David9248/Tofu-Zero/tofuzero/keymaps/default/ANTIGO CONFIG.txt

#define ENCODER_A_PINS { GP9, GP12 }
#define ENCODER_B_PINS { GP10, GP13 }
