David9248/Tofu-Zero/tofuzero/keymaps/vial/keymap.c

#include QMK_KEYBOARD_H

enum layer_names {
    _0,
    _1,
    _2,
    _LAYER_COUNT
};

// === KEYMAPS ===
const uint16_t PROGMEM keymaps[][MATRIX_ROWS][MATRIX_COLS] = {
    [_0] = LAYOUT(
        KC_1,    KC_2,    KC_3,
        KC_4,    KC_5,    KC_6,
        KC_7,    KC_8,    KC_9
    ),

    [_1] = LAYOUT(
        KC_Q,    KC_W,    KC_E,
        KC_A,    KC_S,    KC_D,
        KC_Z,    KC_X,    KC_C
    ),

    [_2] = LAYOUT(
        KC_F1,   KC_F2,   KC_F3,
        KC_F4,   KC_F5,   KC_F6,
        KC_F7,   KC_F8,   KC_F9
    )
};
// === ENCODER (RODA) - CONTROLA DIFERENTES FUNÇÕES POR LAYER ===
#if defined(ENCODER_MAP_ENABLE)
const uint16_t PROGMEM encoder_map[][NUM_ENCODERS][NUM_DIRECTIONS] = {
    [_0] = { ENCODER_CCW_CW(KC_VOLD, KC_VOLU) },
    [_1] = { ENCODER_CCW_CW(KC_BRID, KC_BRIU) },
    [_2]   = { ENCODER_CCW_CW(RGB_RMOD, RGB_MOD) }
};
#endif

// === BOTÃO DO ENCODER (CLIQUE) - MUDA LAYER ===
void keyboard_post_init_user(void) {
    setPinInputHigh(GP15); // Botão no GP15
}

void matrix_scan_user(void) {
    static bool button_pressed = false;
    static uint16_t debounce_timer = 0;
    
    // Lê estado do botão (ativo LOW se usas pull-up)
    bool button_state = !readPin(GP15);
    
    // Debounce de 25ms
    if (button_state != button_pressed) {
        if (timer_elapsed(debounce_timer) > 25) {
            if (button_state) { // Botão premido AGORA
                // MUDAR PARA PRÓXIMA LAYER
                uint8_t current_layer = get_highest_layer(layer_state);
                uint8_t next_layer = (current_layer + 1) % _LAYER_COUNT;
                layer_move(next_layer);
            }
            button_pressed = button_state;
            debounce_timer = timer_read();
        }
    }
}

// === OLED ===
#ifdef OLED_ENABLE

#define FRAME_DURATION 333

uint32_t anim_timer = 0;
uint8_t current_frame = 0;

// Frame 0
static const char PROGMEM frame_0[] = {
0x00, 0x00, 0x00, 0x00, 0x00, 0x00, 0x00, 0x00, 0x00, 0x00, 0x00, 0x00, 0x00, 0x00, 0x00, 0x00, 
0x00, 0x00, 0x00, 0x00, 0x00, 0x00, 0x00, 0x00, 0x00, 0x00, 0x00, 0x00, 0x00, 0x00, 0x00, 0x00, 
0x00, 0x00, 0x00, 0x00, 0x00, 0x00, 0x00, 0x00, 0x00, 0x00, 0x00, 0x00, 0x00, 0x00, 0x00, 0x00, 
0x00, 0x00, 0x00, 0x00, 0x00, 0x00, 0x00, 0x00, 0x00, 0x00, 0x00, 0x00, 0x00, 0x00, 0x00, 0x00, 
0x00, 0x00, 0x00, 0x00, 0x00, 0x00, 0x00, 0x00, 0x00, 0x00, 0x00, 0x00, 0x00, 0x00, 0x00, 0x00, 
0x00, 0x00, 0xc0, 0xe0, 0xf0, 0xe0, 0x80, 0x00, 0x00, 0x00, 0x00, 0x00, 0x00, 0x80, 0xe0, 0xf0, 
0xf8, 0xf0, 0x80, 0x00, 0x00, 0x00, 0x00, 0x00, 0x00, 0x00, 0x00, 0x00, 0x00, 0x00, 0x00, 0x00, 
0x00, 0x00, 0x00, 0x00, 0x00, 0x00, 0x00, 0x00, 0x00, 0x00, 0x00, 0x00, 0x00, 0x00, 0x00, 0x00, 
0x00, 0x00, 0x00, 0x00, 0x00, 0x00, 0x00, 0x00, 0x00, 0x00, 0x00, 0x00, 0x00, 0x00, 0x00, 0x00, 
0x00, 0xff, 0x7f, 0xbf, 0xdf, 0x1f, 0x37, 0x78, 0xfe, 0xf8, 0xfe, 0xf0, 0x67, 0xbf, 0xdf, 0xdf, 
0x1f, 0x3f, 0x7f, 0xfc, 0x00, 0x00, 0x80, 0x00, 0x00, 0x00, 0x00, 0x00, 0x00, 0x00, 0x00, 0x00, 
0x00, 0x00, 0x00, 0x00, 0x00, 0x00, 0x00, 0x00, 0x00, 0x00, 0x00, 0x00, 0x00, 0x00, 0x00, 0x00, 
0x00, 0x00, 0x00, 0x00, 0x00, 0x00, 0x00, 0x00, 0x00, 0x00, 0x00, 0x00, 0x00, 0x00, 0x00, 0x12, 
0x1a, 0x0f, 0x3c, 0x68, 0xe8, 0xf9, 0xf8, 0xfc, 0xd7, 0xe7, 0xd7, 0xdf, 0xfc, 0xf9, 0xe9, 0xe9, 
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
        case _1:
            oled_write_P(PSTR("LAYER 2"), false);
            break;
        case _2:
            oled_write_P(PSTR("LAYER 3"), false);
            break;
        default:
            oled_write_P(PSTR("UNKNOWN"), false);
    }
    
    return false;
}

#endif // OLED_ENABLE
